Joshua-Murray/SlimeVr_18650_PCB_Version/Case Files/Electronic PlaceHolder Parts/GY-91/Decals/GY-91_Top3.jpg

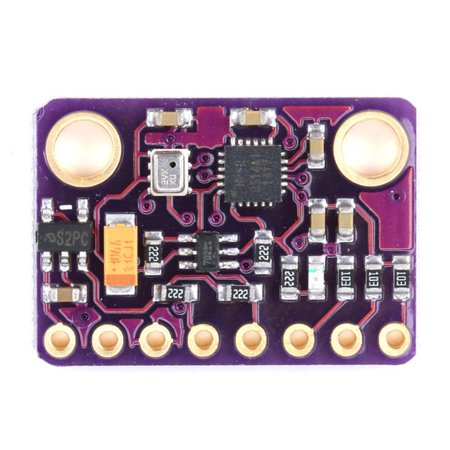
Case Files/Electronic PlaceHolder Parts/GY-91/Decals/GY-91_Top3.jpg
