Joshua-Murray/SlimeVr_18650_PCB_Version/Case Files/Electronic PlaceHolder Parts/GY-91/Renders/GY-91 top - pins down.JPG

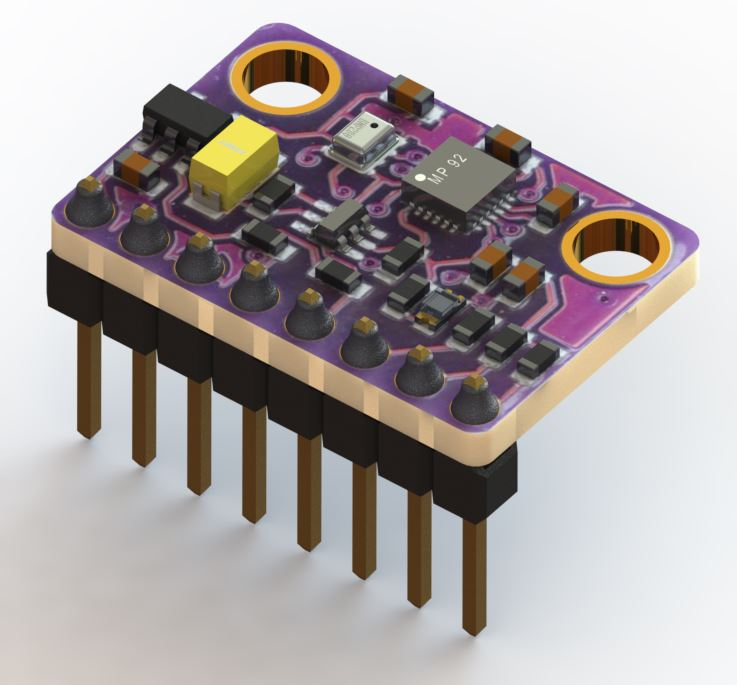
Case Files/Electronic PlaceHolder Parts/GY-91/Renders/GY-91 top - pins down.JPG
