Joshua-Murray/SlimeVr_18650_PCB_Version/Case Files/Vertical 18650 Battery Mount/Original Files/Main_Body_Lid_Hip.SLDPRT

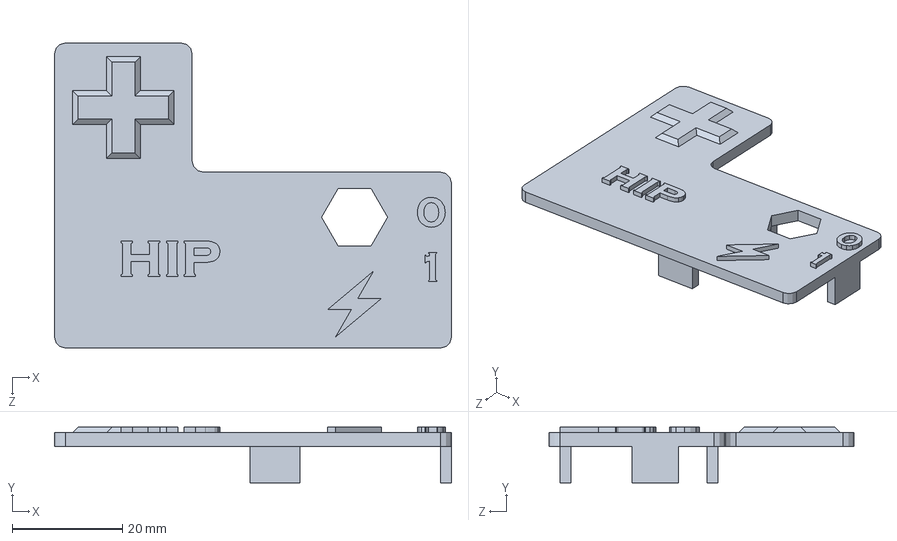
[picture p48: CAD file, 2022-03-08]
Case Files/Vertical 18650 Battery Mount/Original Files/Main_Body_Lid_Hip.SLDPRT
72.1 x 10.1 x 55.4 mm
