Joshua-Murray/SlimeVr_18650_PCB_Version/Case Files/Electronic PlaceHolder Parts/TP4056_TC.SLDASM

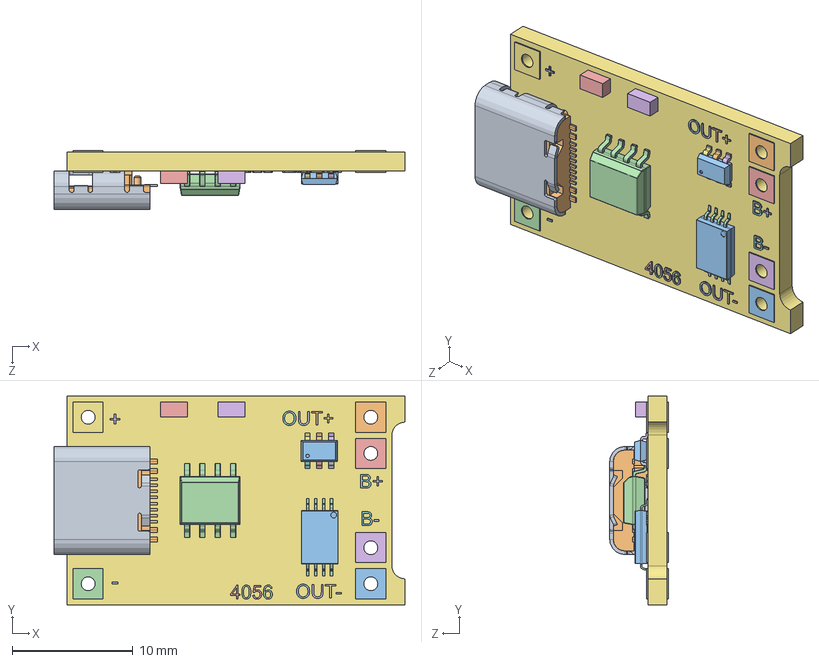
[picture p49: CAD file, 2022-03-08]
Case Files/Electronic PlaceHolder Parts/TP4056_TC.SLDASM
29.1 x 17.3 x 4.86 mm
Shroud.step
Plastic Body & Connector.step
ATiny45_Body.step
ATiny45_Pin.step x 8
Pin2.step
Pin4.step
Pin6.step
Pin1.step
Pin3.step
Pin5.step
Body.step
IC SMD 8 Pins.step
Semiconductors-0.step
Semiconductors-1.step
PCB-2.step
PCB-3.step
PCB-4.step
PCB-5.step
PCB-6.step
PCB-7.step
PCB-8.step
PCB-9.step
PCB-10.step
PCB-11.step
PCB-12.step
PCB-13.step
PCB-14.step
PCB-15.step
PCB-16.step
PCB-17.step
PCB-18.step
PCB-19.step
PCB-20.step
PCB-21.step
PCB-22.step
PCB-23.step
PCB-24.step
PCB-25.step
PCB-26.step
PCB-27.step
PCB-28.step
PCB-29.step
PCB-30.step
PCB-31.step
PCB-32.step
