Joshua-Murray/SlimeVr_18650_PCB_Version/Case Files/Horizontal 18650 Battery Mount/_Main_Body_Lid_RAnkle.STL

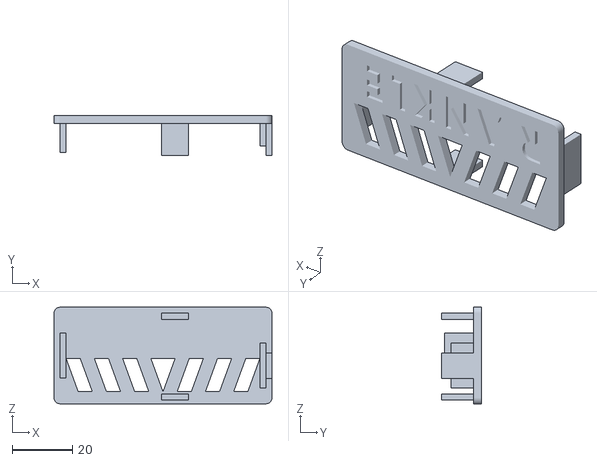
[picture p50: CAD file, 2022-03-08]
Case Files/Horizontal 18650 Battery Mount/_Main_Body_Lid_RAnkle.STL
72.1 x 13.1 x 32.0
