Joshua-Murray/SlimeVr_18650_PCB_Version/Case Files/Electronic PlaceHolder Parts/wemos-d1-mini-more-accurate-version-1.snapshot.3/Wemos_d1_mini-detailed_assembly.SLDASM

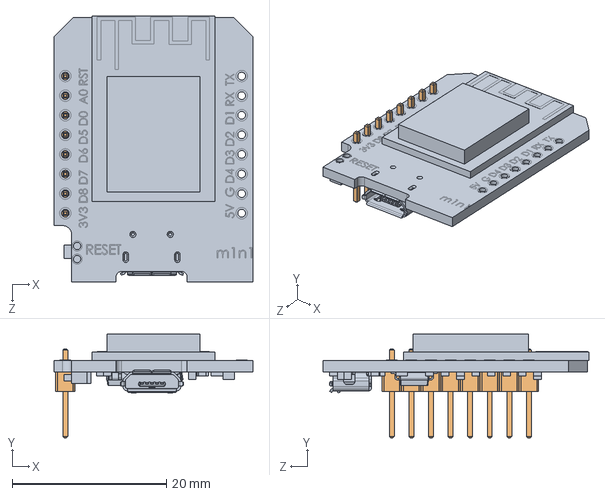
[picture p51: CAD file, 2022-03-08]
Case Files/Electronic PlaceHolder Parts/wemos-d1-mini-more-accurate-version-1.snapshot.3/Wemos_d1_mini-detailed_assembly.SLDASM
25.8 x 13.4 x 34.4 mm
