Joshua-Murray/SlimeVr_18650_PCB_Version/Case Files/Electronic PlaceHolder Parts/MPU_6050.SLDASM

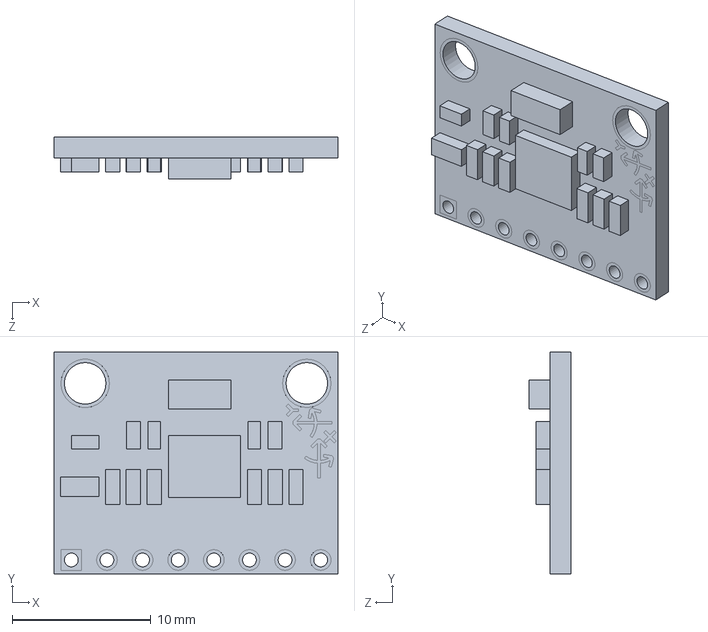
[picture p52: CAD file, 2022-03-08]
Case Files/Electronic PlaceHolder Parts/MPU_6050.SLDASM
20.5 x 16.0 x 3.00 mm
