Joshua-Murray/SlimeVr_18650_PCB_Version/Case Files/Electronic PlaceHolder Parts/GY-91/Components/SOT23-5.SLDPRT

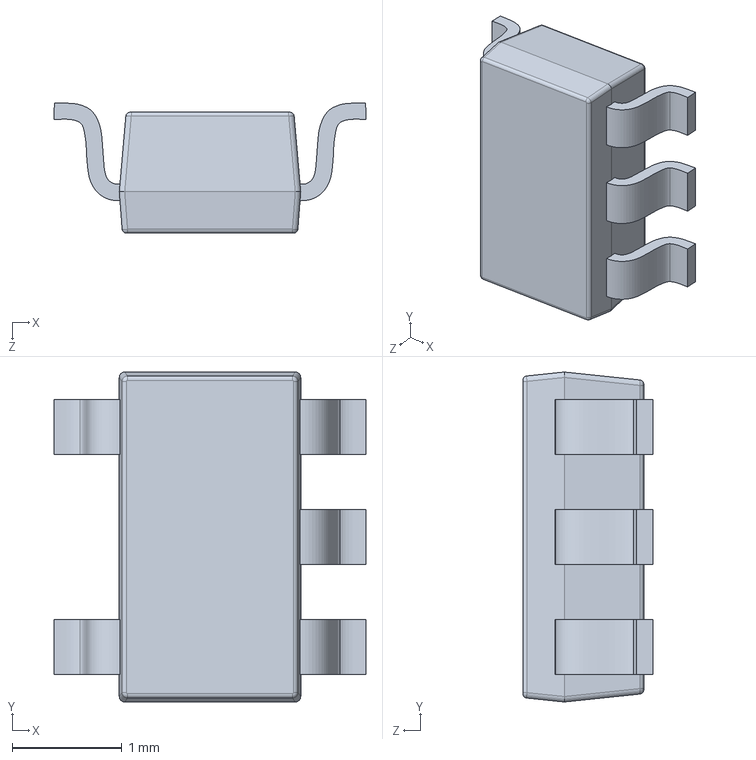
[picture p53: CAD file, 2022-03-08]
Case Files/Electronic PlaceHolder Parts/GY-91/Components/SOT23-5.SLDPRT
2.84 x 3.00 x 1.18 mm
