Joshua-Murray/SlimeVr_18650_PCB_Version/Case Files/Electronic PlaceHolder Parts/wemos-d1-mini-more-accurate-version-1.snapshot.3/push_button.SLDPRT

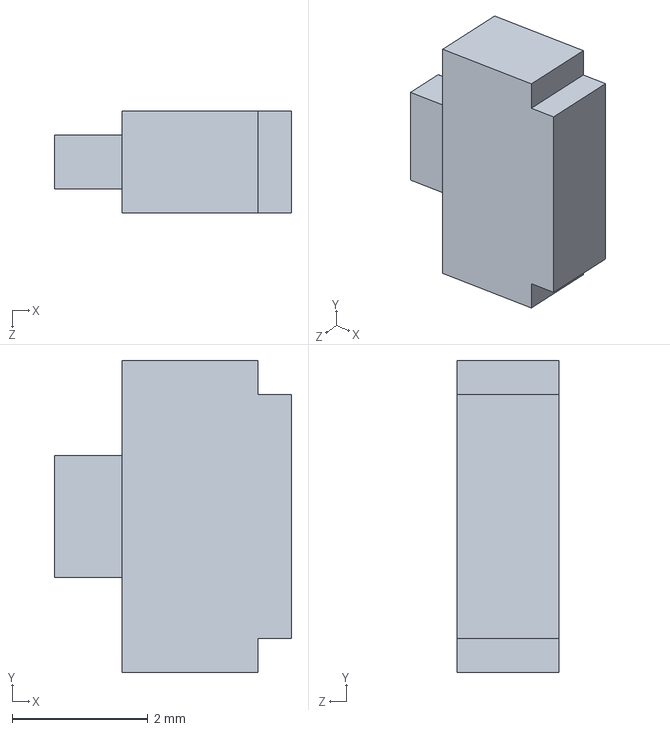
[picture p54: CAD file, 2022-03-08]
Case Files/Electronic PlaceHolder Parts/wemos-d1-mini-more-accurate-version-1.snapshot.3/push_button.SLDPRT
3.50 x 4.60 x 1.50 mm
