Joshua-Murray/SlimeVr_18650_PCB_Version/Case Files/Extension Case/_Aux Lid.STL

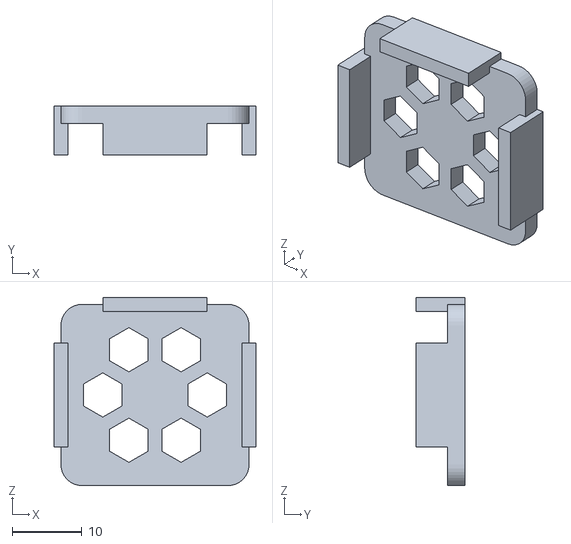
[picture p55: CAD file, 2022-03-08]
Case Files/Extension Case/_Aux Lid.STL
29.0 x 7.00 x 27.0
