Joshua-Murray/SlimeVr_18650_PCB_Version/Case Files/Extension Case/Original Files/Extension Case Lid.SLDPRT

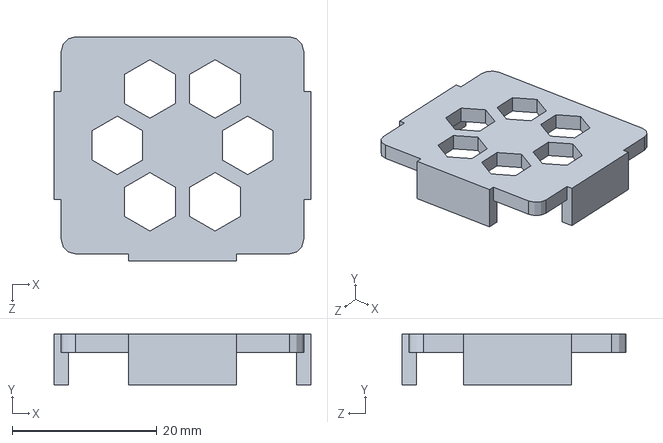
[picture p56: CAD file, 2022-03-08]
Case Files/Extension Case/Original Files/Extension Case Lid.SLDPRT
35.5 x 7.00 x 31.0 mm
