Joshua-Murray/SlimeVr_18650_PCB_Version/Case Files/Electronic PlaceHolder Parts/GY-91/Components/Backup (1) of SOT23-6-1.sldprt

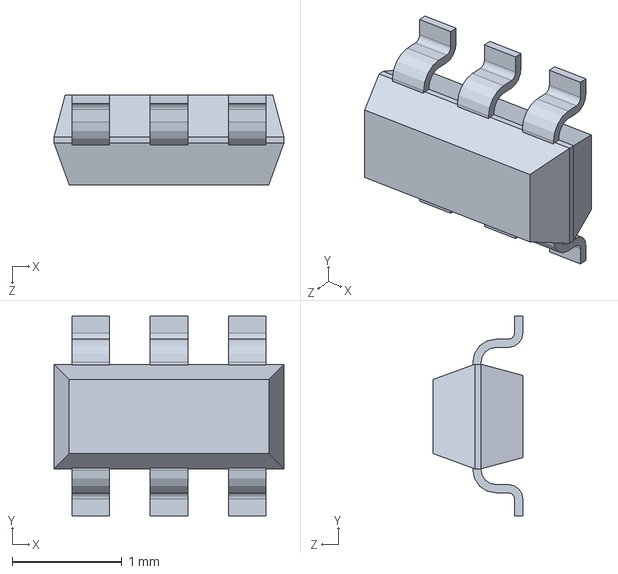
[picture p57: CAD file, 2022-03-08]
Case Files/Electronic PlaceHolder Parts/GY-91/Components/Backup (1) of SOT23-6-1.sldprt
2.10 x 1.82 x 0.819 mm
