Joshua-Murray/SlimeVr_18650_PCB_Version/Case Files/Electronic PlaceHolder Parts/ProtoBoard.SLDPRT

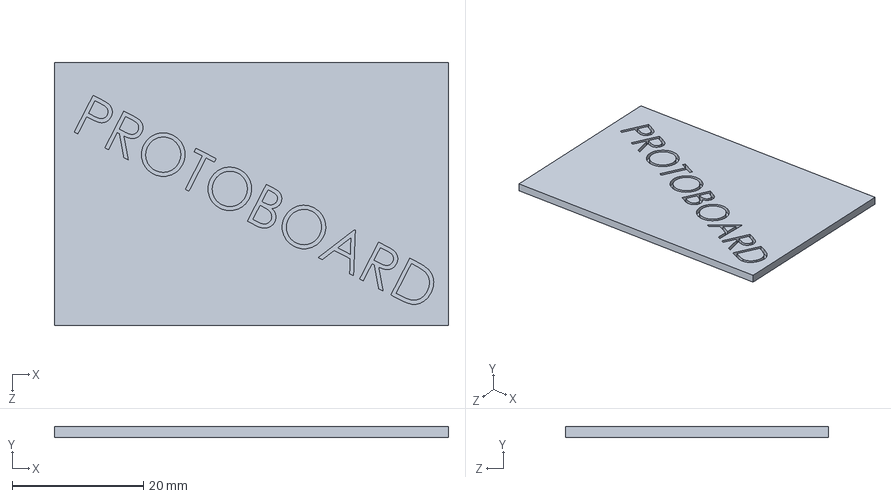
[picture p58: CAD file, 2022-03-08]
Case Files/Electronic PlaceHolder Parts/ProtoBoard.SLDPRT
60.0 x 1.60 x 40.0 mm
