Joshua-Murray/SlimeVr_18650_PCB_Version/Case Files/Electronic PlaceHolder Parts/wemos-d1-mini-more-accurate-version-1.snapshot.3/WEMOS-D1-mini_detailed.SLDPRT

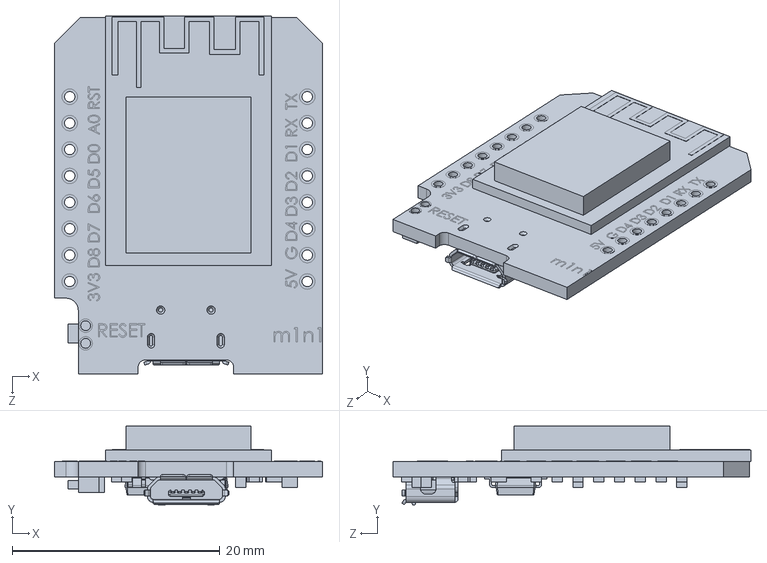
[picture p59: CAD file, 2022-03-08]
Case Files/Electronic PlaceHolder Parts/wemos-d1-mini-more-accurate-version-1.snapshot.3/WEMOS-D1-mini_detailed.SLDPRT
25.8 x 7.60 x 34.4 mm
