Joshua-Murray/SlimeVr_18650_PCB_Version/Case Files/Extension Case/_Aux Body.STL

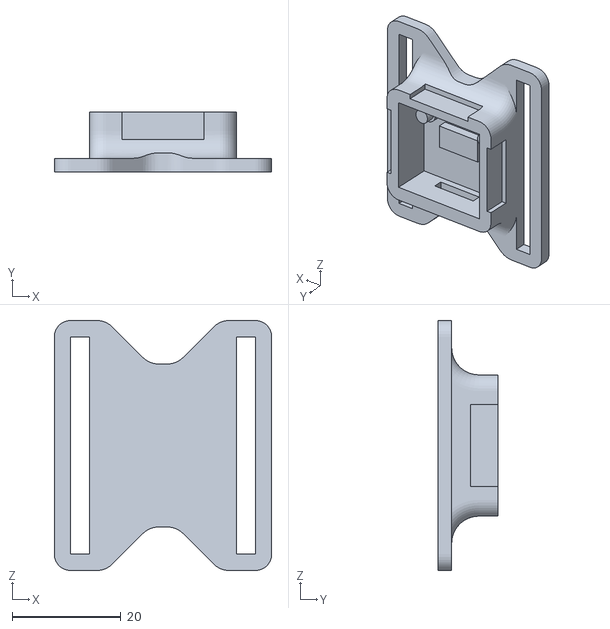
[picture p60: CAD file, 2022-03-08]
Case Files/Extension Case/_Aux Body.STL
40.0 x 11.0 x 46.0
