Joshua-Murray/SlimeVr_18650_PCB_Version/Case Files/Electronic PlaceHolder Parts/GY-91/Components/Surface Mount Chip LED 3.2x1.6mm.SLDPRT

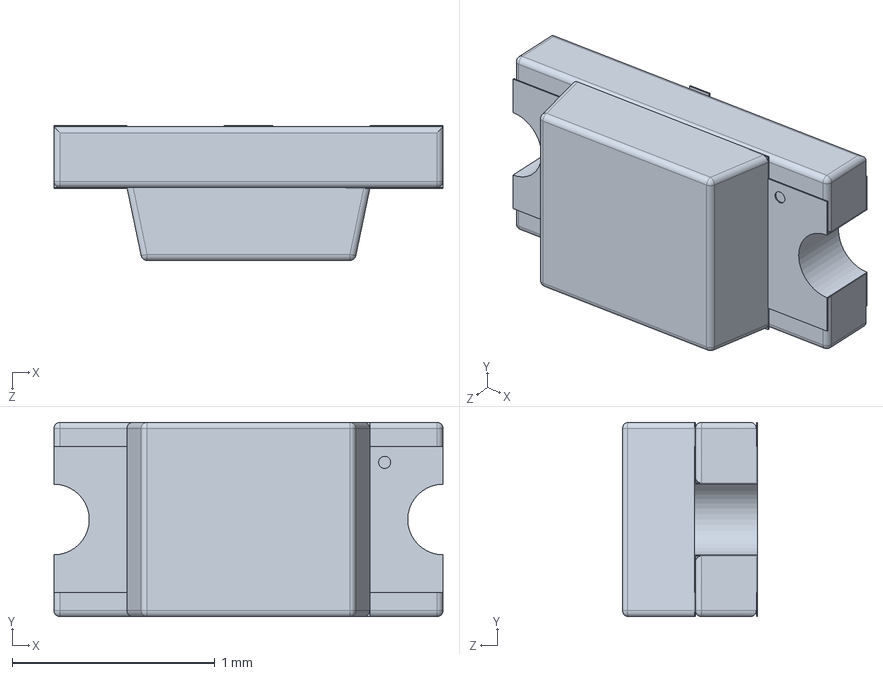
[picture p61: CAD file, 2022-03-08]
Case Files/Electronic PlaceHolder Parts/GY-91/Components/Surface Mount Chip LED 3.2x1.6mm.SLDPRT
1.92 x 0.96 x 0.666 mm
