Joshua-Murray/SlimeVr_18650_PCB_Version/Case Files/Electronic PlaceHolder Parts/Mini-Black Breadboard.SLDPRT

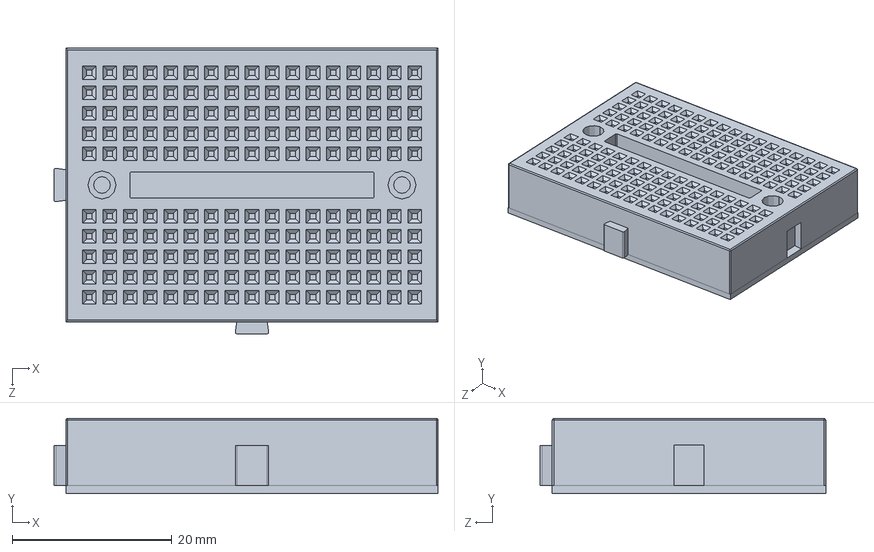
[picture p62: CAD file, 2022-03-08]
Case Files/Electronic PlaceHolder Parts/Mini-Black Breadboard.SLDPRT
48.0 x 9.40 x 35.7 mm
