Joshua-Murray/SlimeVr_18650_PCB_Version/Case Files/Electronic PlaceHolder Parts/wemos-d1-mini-more-accurate-version-1.snapshot.3/usb socket.SLDPRT

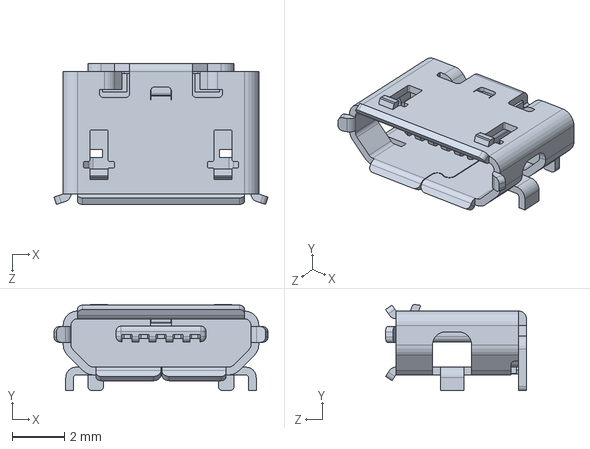
[picture p63: CAD file, 2022-03-08]
Case Files/Electronic PlaceHolder Parts/wemos-d1-mini-more-accurate-version-1.snapshot.3/usb socket.SLDPRT
8.20 x 3.30 x 5.40 mm
