Joshua-Murray/SlimeVr_18650_PCB_Version/Case Files/Electronic PlaceHolder Parts/GY-91/Components/MPU9250.sldprt

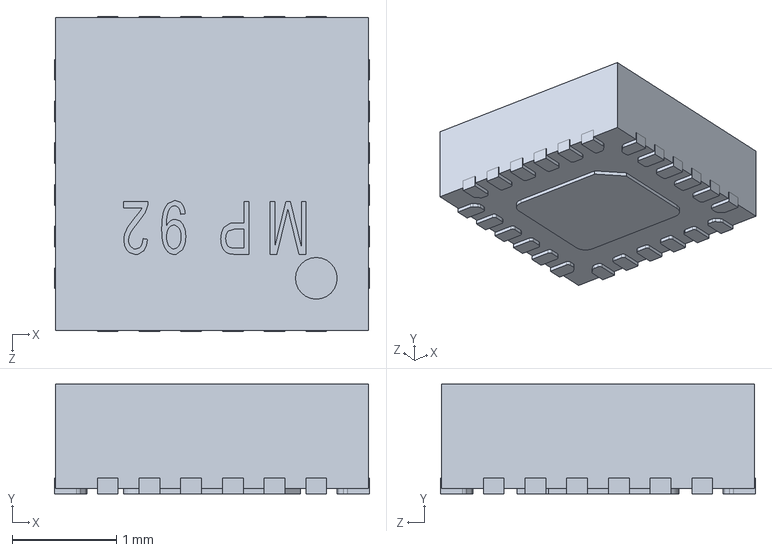
[picture p64: CAD file, 2022-03-08]
Case Files/Electronic PlaceHolder Parts/GY-91/Components/MPU9250.sldprt
3.02 x 1.05 x 3.02 mm
