Joshua-Murray/SlimeVr_18650_PCB_Version/Case Files/Electronic PlaceHolder Parts/ICM 20948 Placeholder.SLDPRT

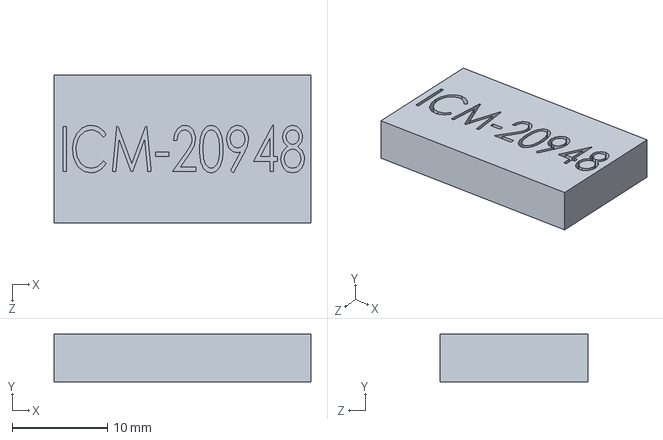
[picture p65: CAD file, 2022-03-08]
Case Files/Electronic PlaceHolder Parts/ICM 20948 Placeholder.SLDPRT
27.0 x 5.00 x 15.5 mm
