Joshua-Murray/SlimeVr_18650_PCB_Version/Case Files/Electronic PlaceHolder Parts/wemos-d1-mini-more-accurate-version-1.snapshot.3/SOIC_16_ch340.SLDPRT

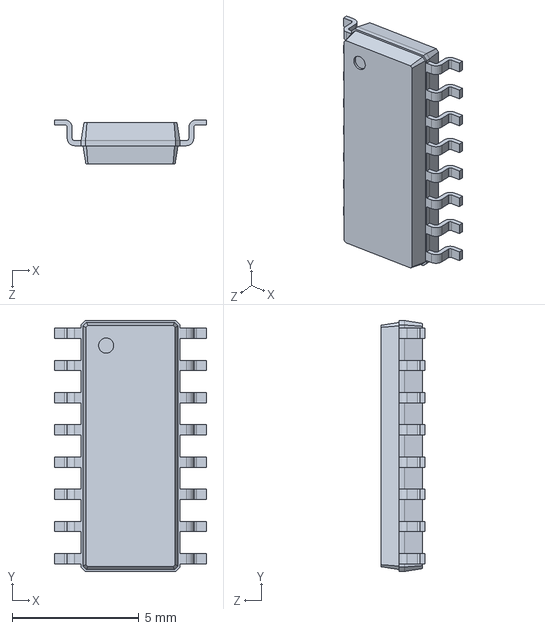
[picture p66: CAD file, 2022-03-08]
Case Files/Electronic PlaceHolder Parts/wemos-d1-mini-more-accurate-version-1.snapshot.3/SOIC_16_ch340.SLDPRT
6.00 x 9.90 x 1.75 mm
