Joshua-Murray/SlimeVr_18650_PCB_Version/Case Files/Electronic PlaceHolder Parts/GY-91/Components/Backup (1) of BMP280.SLDPRT

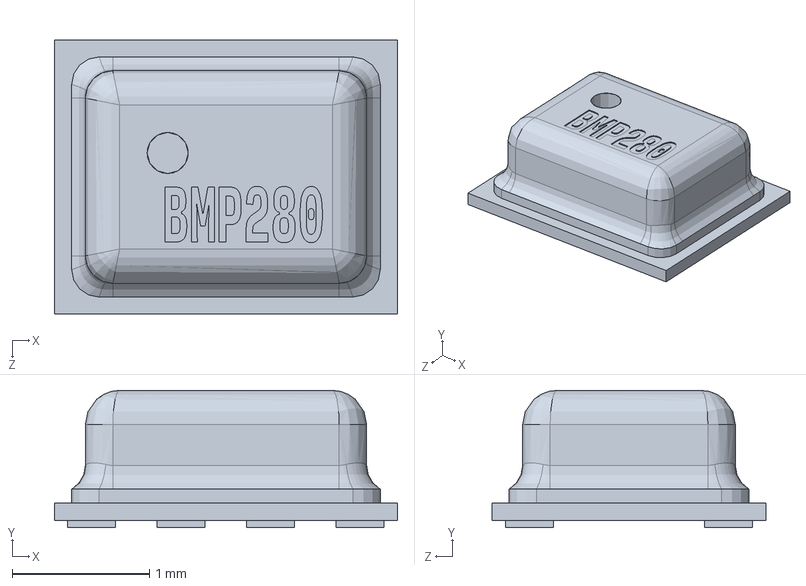
[picture p67: CAD file, 2022-03-08]
Case Files/Electronic PlaceHolder Parts/GY-91/Components/Backup (1) of BMP280.SLDPRT
2.50 x 1.00 x 2.00 mm
