Joshua-Murray/SlimeVr_18650_PCB_Version/Case Files/Electronic PlaceHolder Parts/wemos-d1-mini-more-accurate-version-1.snapshot.3/Pin_header_str_1x08_p2_54mm.sldprt

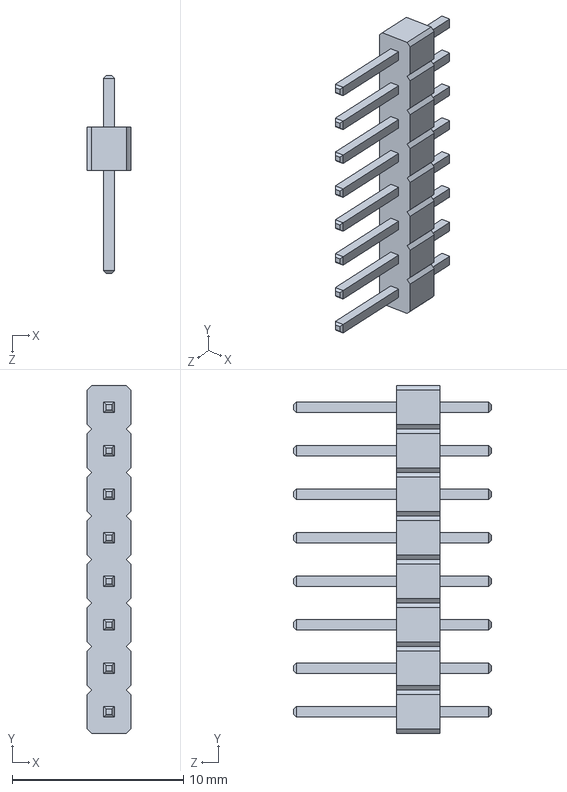
[picture p68: CAD file, 2022-03-08]
Case Files/Electronic PlaceHolder Parts/wemos-d1-mini-more-accurate-version-1.snapshot.3/Pin_header_str_1x08_p2_54mm.sldprt
2.54 x 20.3 x 11.5 mm
