Joshua-Murray/SlimeVr_18650_PCB_Version/Case Files/Electronic PlaceHolder Parts/GY-91/Components/cap_603.SLDPRT

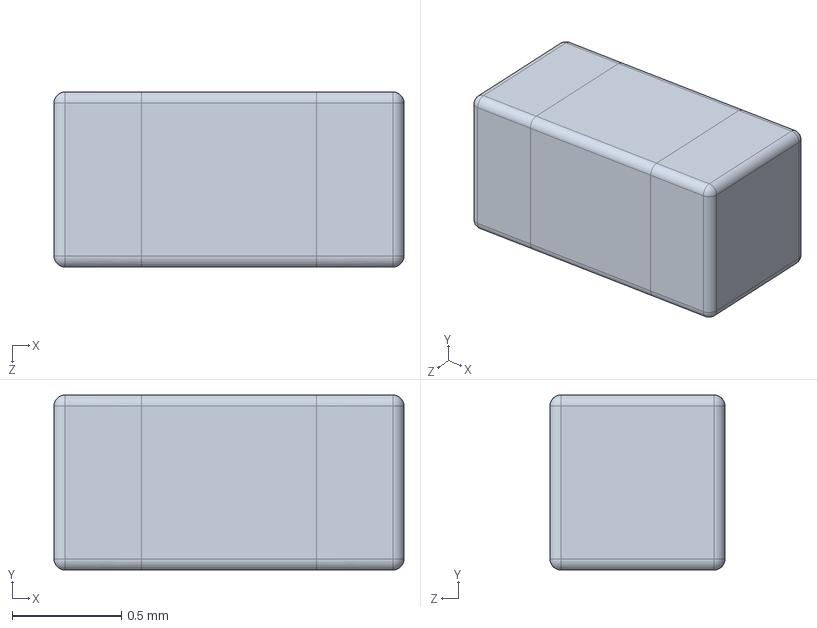
[picture p69: CAD file, 2022-03-08]
Case Files/Electronic PlaceHolder Parts/GY-91/Components/cap_603.SLDPRT
1.60 x 0.8 x 0.8 mm
