Joshua-Murray/SlimeVr_18650_PCB_Version/Case Files/Electronic PlaceHolder Parts/Battery.SLDPRT

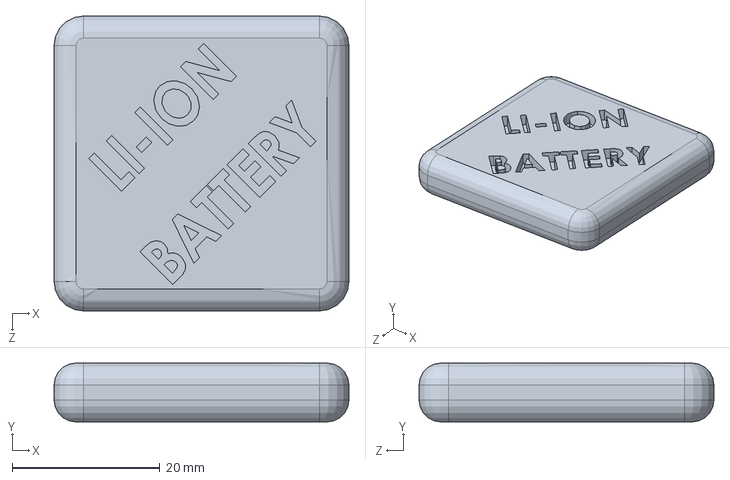
[picture p70: CAD file, 2022-03-08]
Case Files/Electronic PlaceHolder Parts/Battery.SLDPRT
40.0 x 8.00 x 40.0 mm
