Joshua-Murray/SlimeVr_18650_PCB_Version/Case Files/Electronic PlaceHolder Parts/GY-91/Components/Pin Header 1x8 TH Pitch 2.54mm.SLDPRT

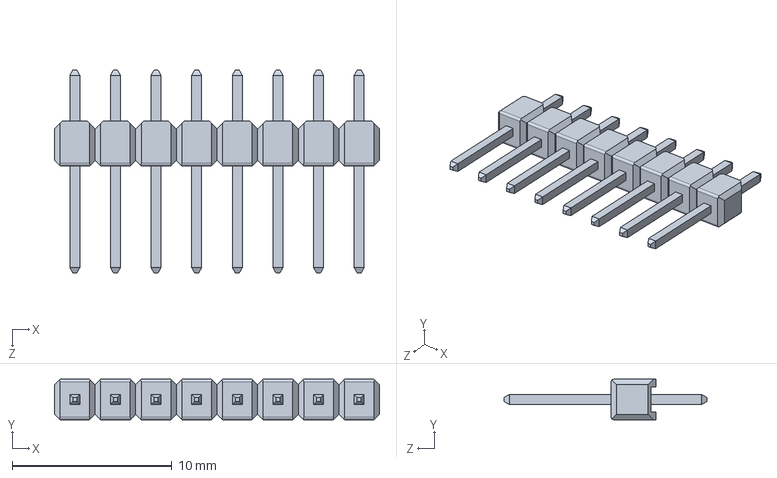
[picture p72: CAD file, 2022-03-08]
Case Files/Electronic PlaceHolder Parts/GY-91/Components/Pin Header 1x8 TH Pitch 2.54mm.SLDPRT
20.3 x 2.54 x 12.7 mm
