Joshua-Murray/SlimeVr_18650_PCB_Version/Case Files/Electronic PlaceHolder Parts/GY-91/Components/GY-91 Base.SLDPRT

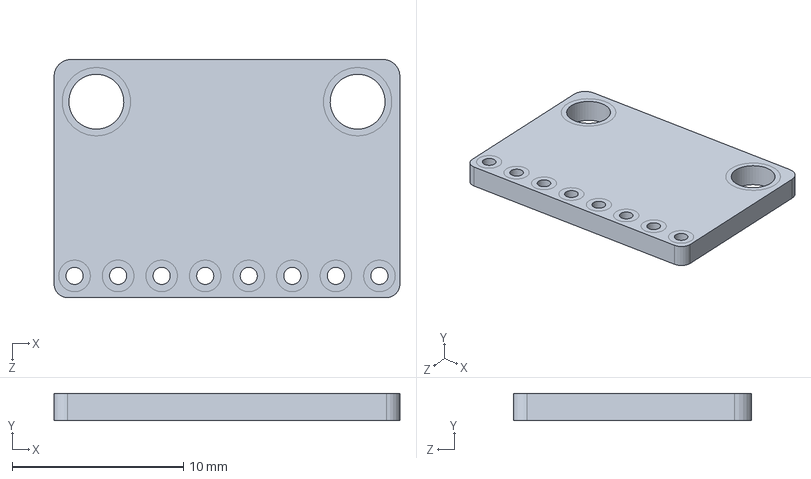
[picture p73: CAD file, 2022-03-08]
Case Files/Electronic PlaceHolder Parts/GY-91/Components/GY-91 Base.SLDPRT
20.2 x 1.60 x 13.9 mm
