Joshua-Murray/SlimeVr_18650_PCB_Version/Case Files/Electronic PlaceHolder Parts/GY-91/Components/Backup (1) of T10uF.SLDPRT

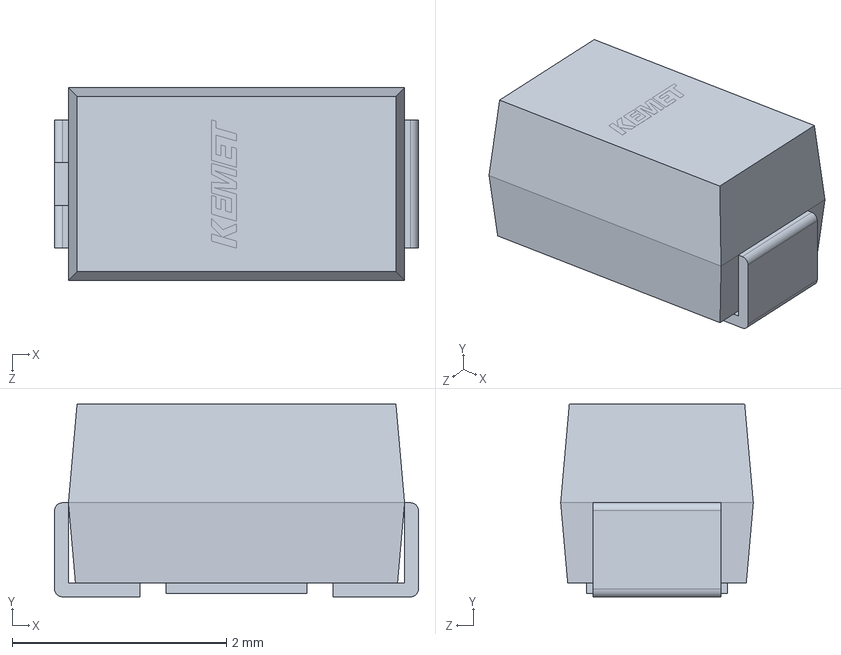
[picture p74: CAD file, 2022-03-08]
Case Files/Electronic PlaceHolder Parts/GY-91/Components/Backup (1) of T10uF.SLDPRT
3.40 x 1.80 x 1.80 mm
