Joshua-Murray/SlimeVr_18650_PCB_Version/Case Files/Electronic PlaceHolder Parts/GY-91/Components/solder.SLDPRT

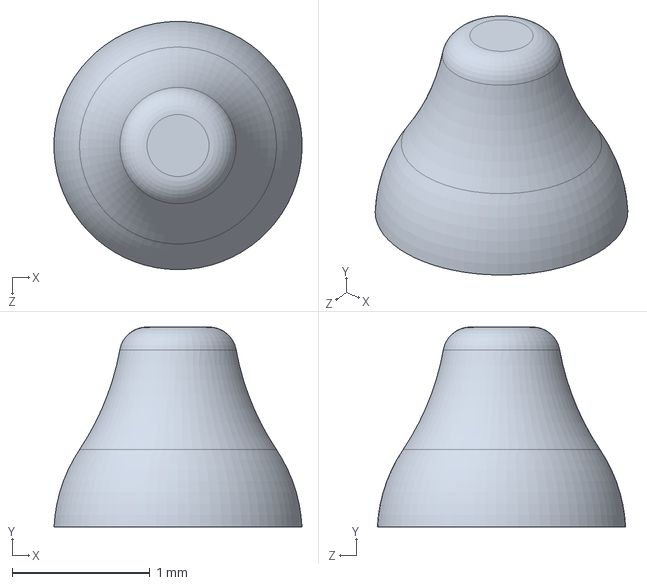
[picture p75: CAD file, 2022-03-08]
Case Files/Electronic PlaceHolder Parts/GY-91/Components/solder.SLDPRT
1.80 x 1.45 x 1.80 mm
